timmit99/Voron_Zero_RGB_Side_Panels/Images/Basic_Wiring _Overview.jpg

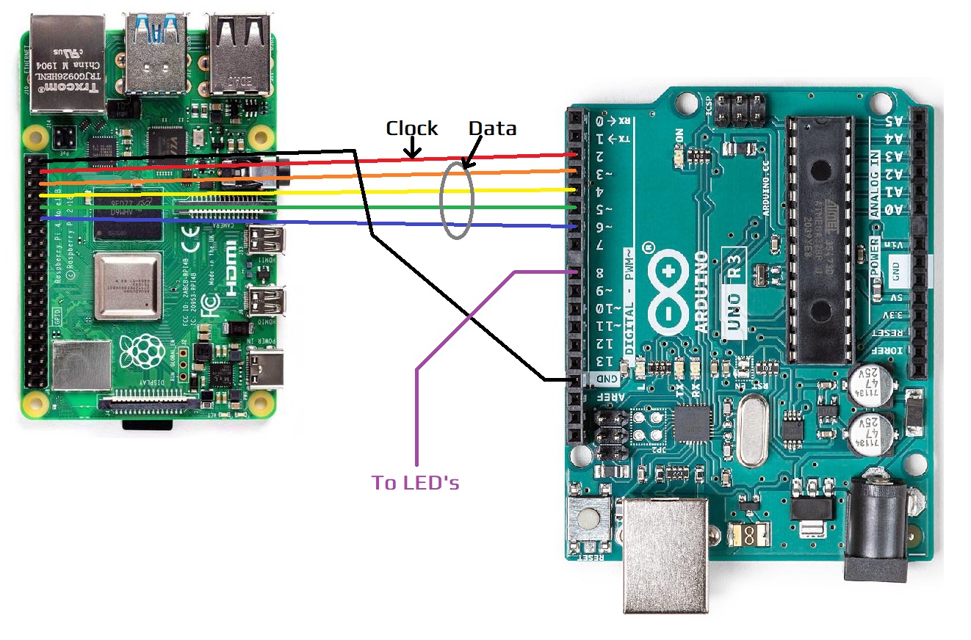
Images/Basic_Wiring _Overview.jpg
